Retrodolivo/Nixie-clock/Software/RGB_Nixie/RGB_Nixie/main.h

#ifndef MAIN_H_
#define MAIN_H_

#define F_CPU 8000000UL

#include <avr/io.h>
#include <avr/interrupt.h>
#include <util/delay.h>
#include <stdio.h>
#include <stdlib.h>

#include "rgb.h"
#include "spi.h"
#include "adc3201.h"


#endif /* MAIN_H_ */
